rabs664/Amstrad-CPC-8255-PIO/Images/Amstrad-CPC-8255-PIO-Test-1-1-SCH.png

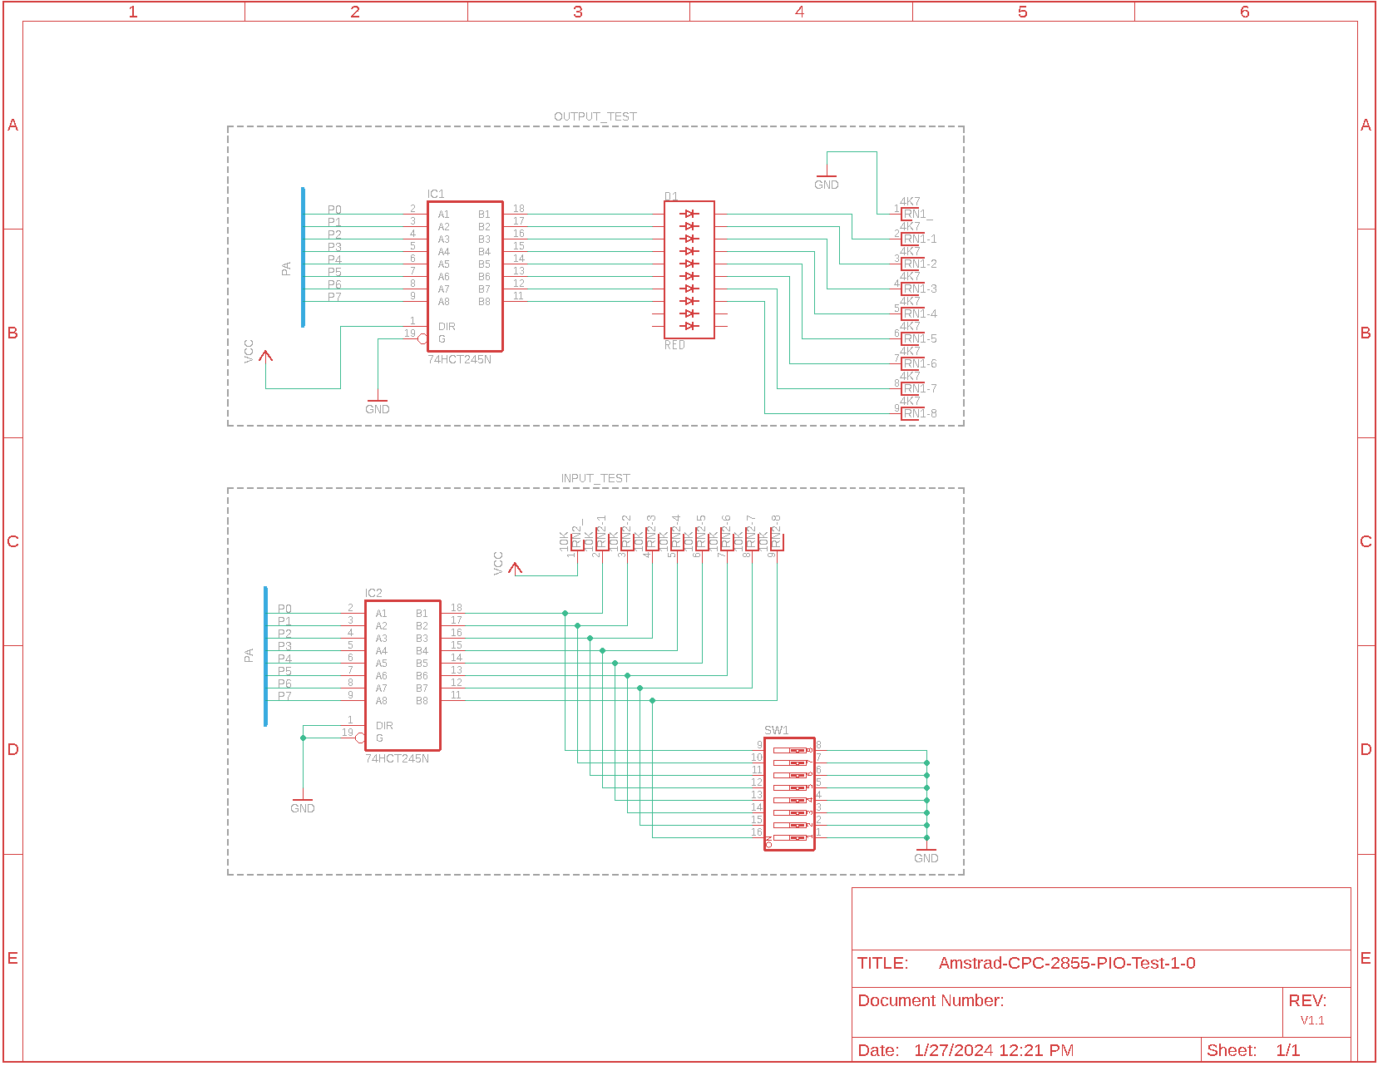
Images/Amstrad-CPC-8255-PIO-Test-1-1-SCH.png
