rabs664/Amstrad-CPC-8255-PIO/Images/board-on-test.jpg

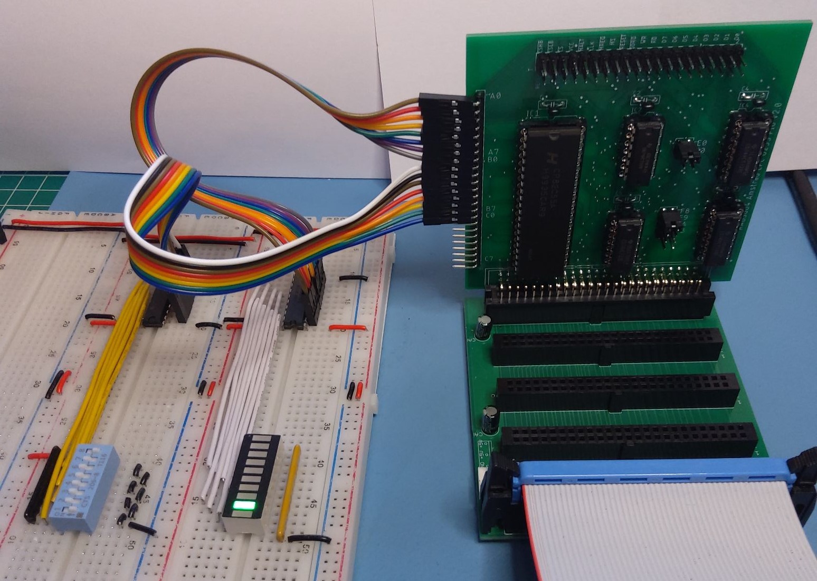
Images/board-on-test.jpg
