rabs664/Amstrad-CPC-8255-PIO/Images/test-breadboard-connected-to-v3-1.jpg

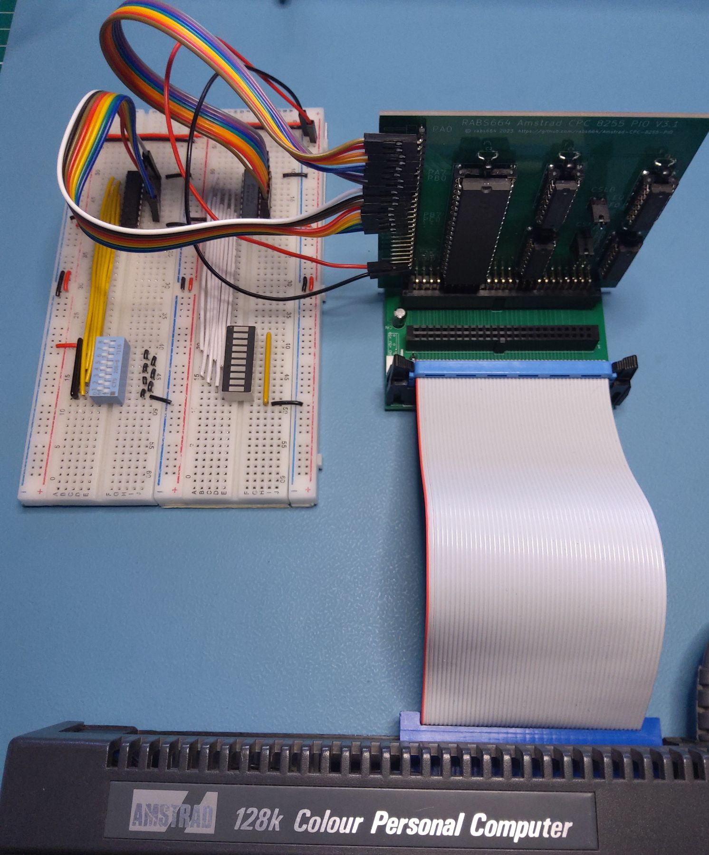
Images/test-breadboard-connected-to-v3-1.jpg
