rabs664/Amstrad-CPC-8255-PIO/Images/test-breadboard.jpg

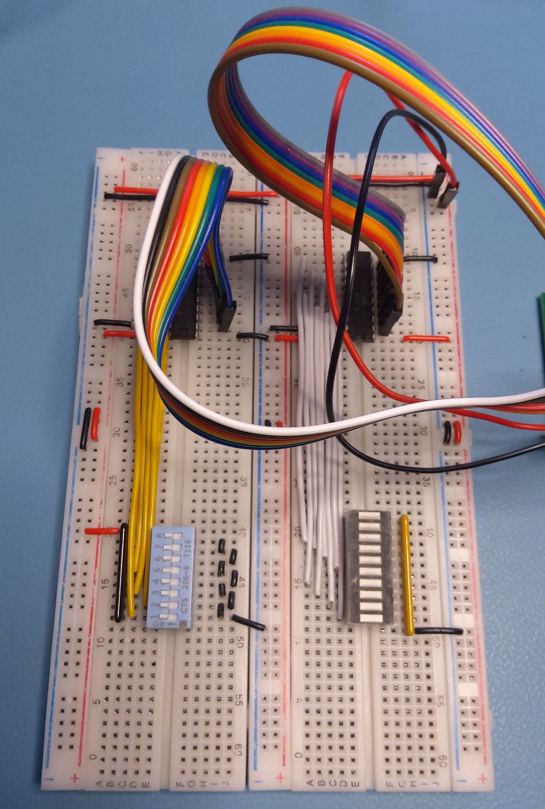
Images/test-breadboard.jpg
